Intrinsically-Sublime/Jack-in-the-box/Individual_files/Crank_gear.stl

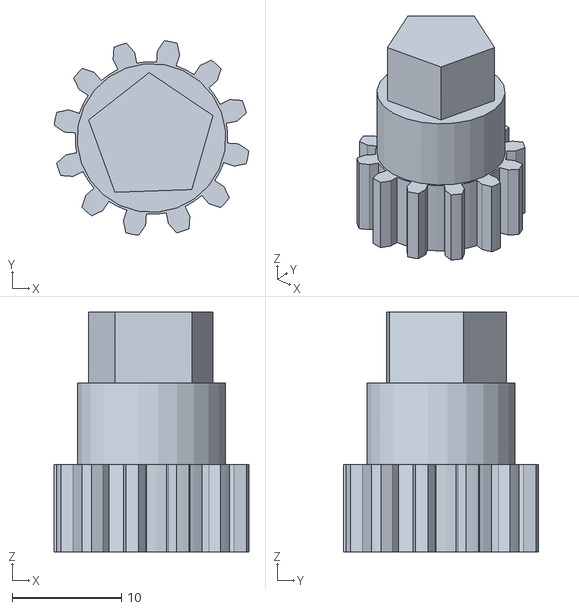
[picture p17: CAD file, 2012-02-15]
Individual_files/Crank_gear.stl
17.8 x 17.8 x 22.0
