Intrinsically-Sublime/Jack-in-the-box/Elastic_spring/Piston_clip.stl

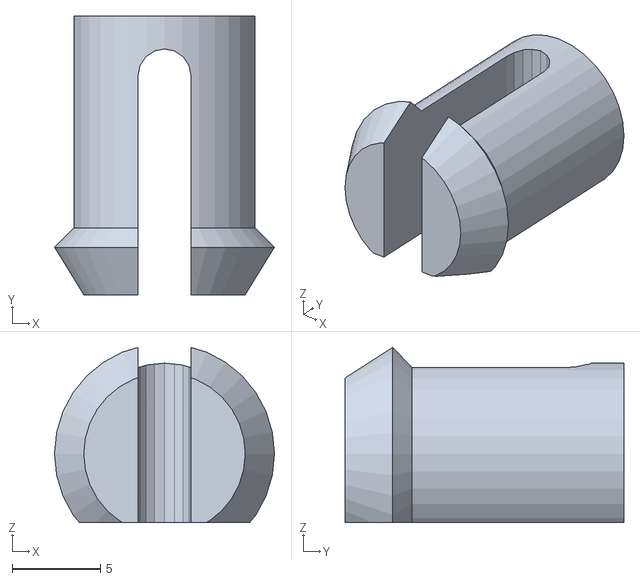
[picture p18: CAD file, 2012-02-15]
Elastic_spring/Piston_clip.stl
12.5 x 15.8 x 9.93
