Intrinsically-Sublime/Jack-in-the-box/Individual_files/Cam_gear_shaft.stl

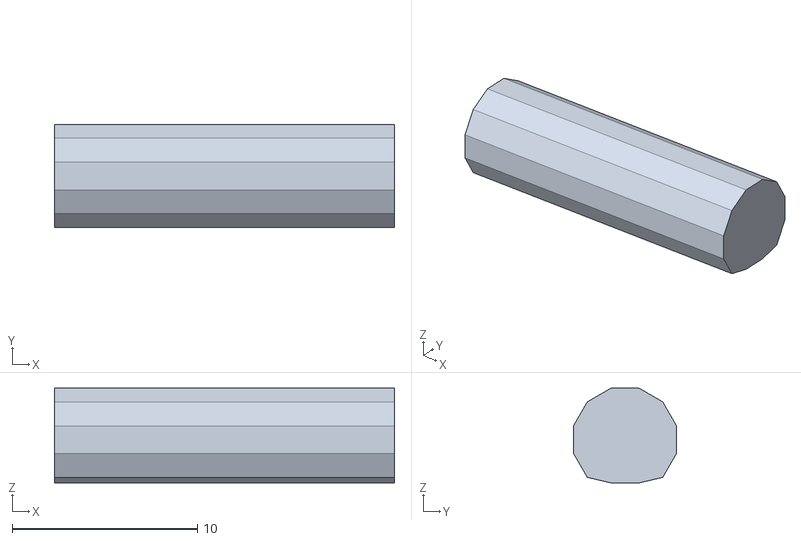
[picture p19: CAD file, 2012-02-15]
Individual_files/Cam_gear_shaft.stl
18.4 x 5.56 x 5.12
