Intrinsically-Sublime/Jack-in-the-box/Individual_files/Compond_gear.stl

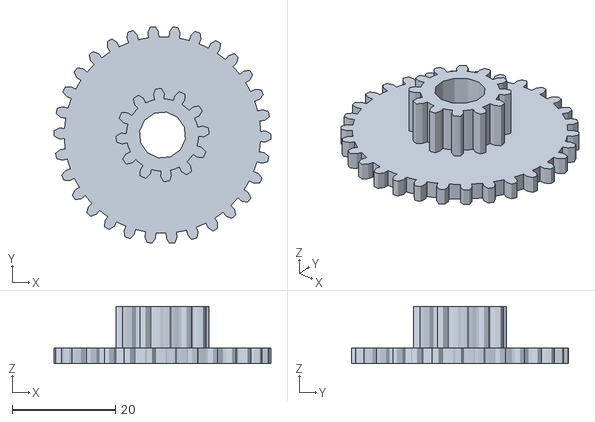
[picture p20: CAD file, 2012-02-15]
Individual_files/Compond_gear.stl
42.0 x 41.9 x 11.1
