Intrinsically-Sublime/Jack-in-the-box/Individual_files/Spring_2.stl

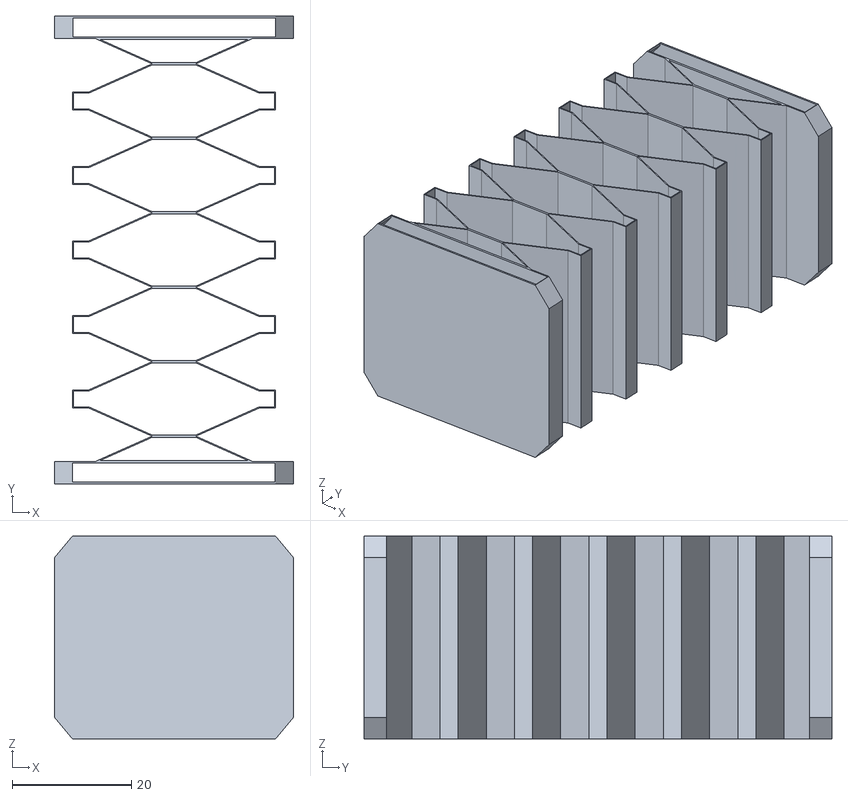
[picture p22: CAD file, 2012-02-15]
Individual_files/Spring_2.stl
40.1 x 78.5 x 34.0
