Intrinsically-Sublime/Jack-in-the-box/Individual_files/Cam_gear.stl

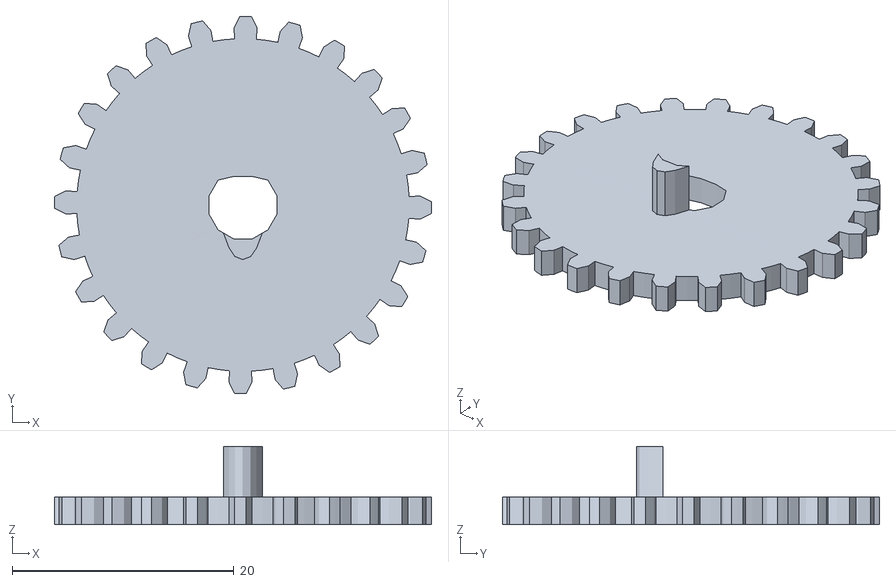
[picture p23: CAD file, 2012-02-15]
Individual_files/Cam_gear.stl
34.0 x 34.0 x 7.04
