Intrinsically-Sublime/Jack-in-the-box/Individual_files/Latch_arm.stl

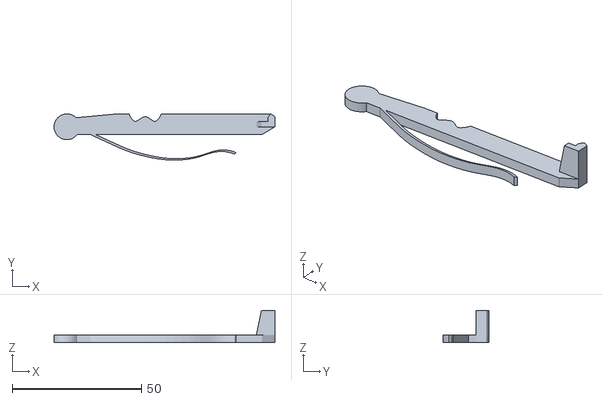
[picture p24: CAD file, 2012-02-15]
Individual_files/Latch_arm.stl
85.5 x 17.9 x 12.4
