Intrinsically-Sublime/Jack-in-the-box/Individual_files/Crank.stl

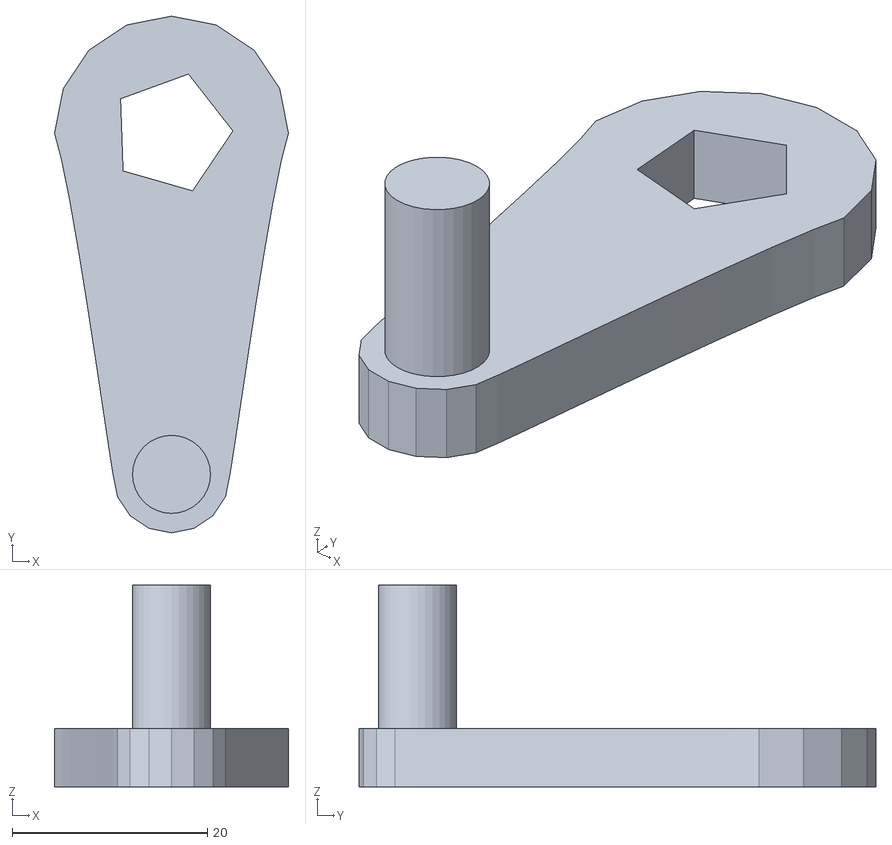
[picture p25: CAD file, 2012-02-15]
Individual_files/Crank.stl
24.0 x 53.0 x 20.7
